Gflinois/split-keyboard/keycap-set/not mine/Row 2 Tab+.stl

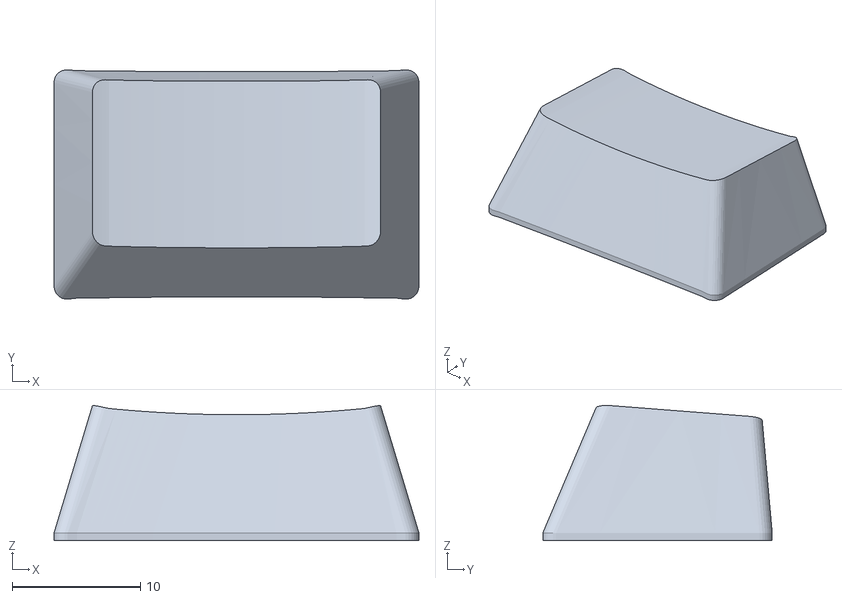
[picture p16: CAD file, 2023-04-18]
keycap-set/not mine/Row 2 Tab+.stl
28.5 x 17.9 x 10.5
