Gflinois/split-keyboard/keycap-set/not mine/Row 3.stl

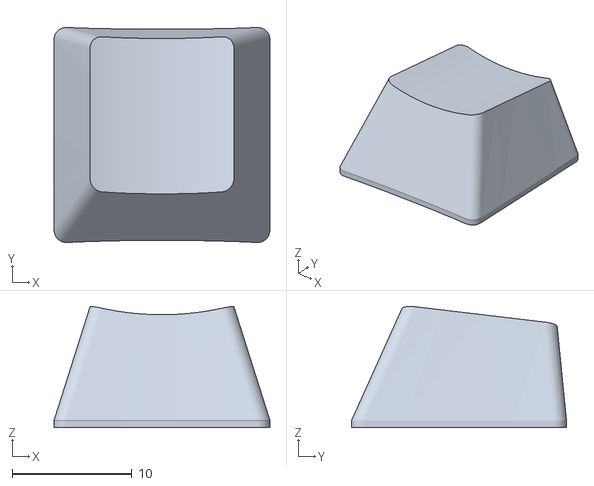
[picture p17: CAD file, 2023-04-18]
keycap-set/not mine/Row 3.stl
18.0 x 17.9 x 10.1
