Gflinois/split-keyboard/keycap-set/not mine/Row 4 Bottom.stl

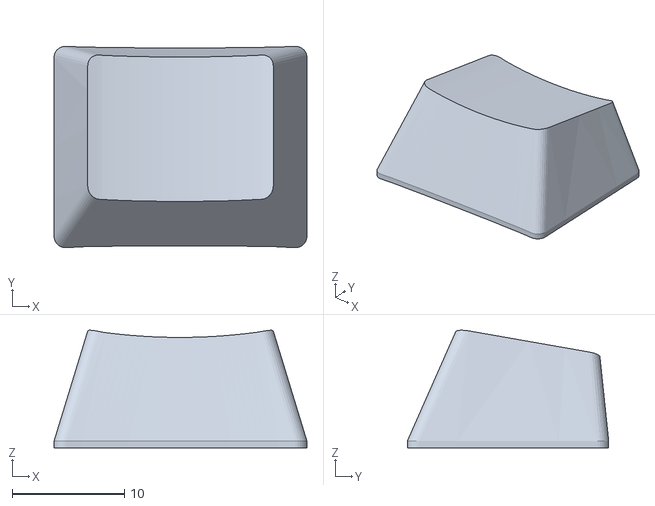
[picture p18: CAD file, 2023-04-18]
keycap-set/not mine/Row 4 Bottom.stl
22.5 x 17.9 x 10.5
