Gflinois/split-keyboard/keycap-set/not mine/Row 4 Spacebar.stl

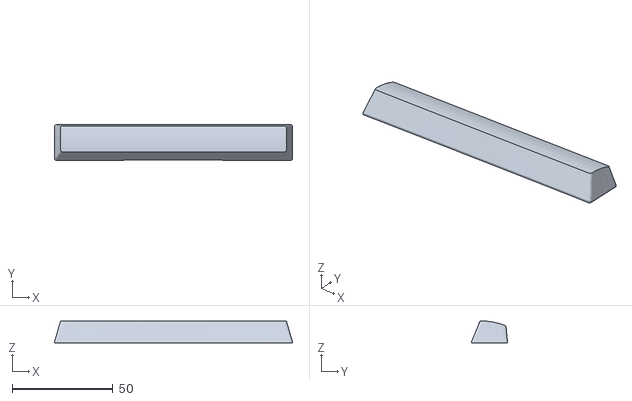
[picture p19: CAD file, 2023-04-18]
keycap-set/not mine/Row 4 Spacebar.stl
118.0 x 17.9 x 10.9
